LMerbecks/D38999-3MF/images/A_Shells_disconnected.jpeg

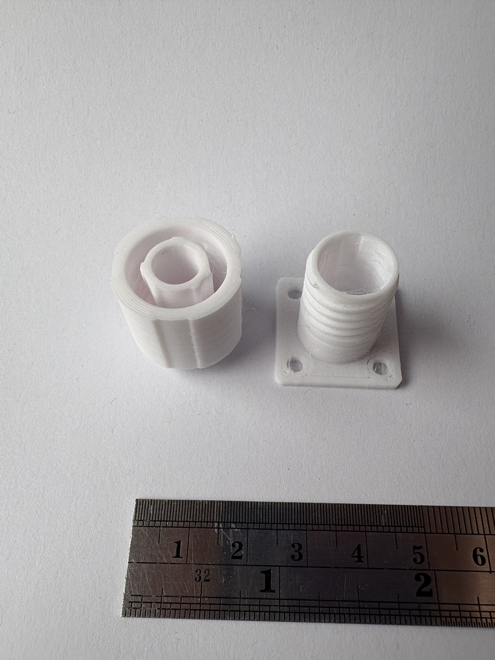
images/A_Shells_disconnected.jpeg
