LMerbecks/D38999-3MF/images/A_Shells_Mating_Dimensions.png

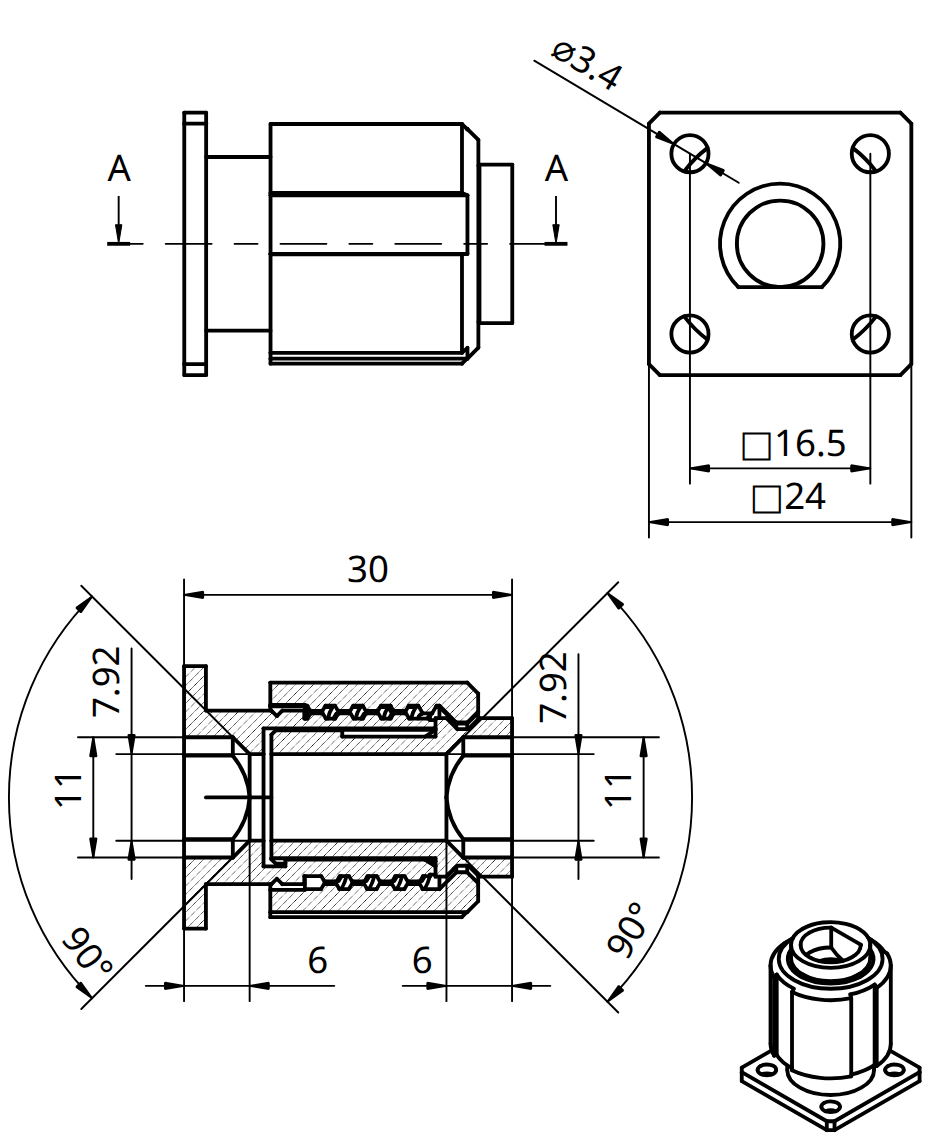
images/A_Shells_Mating_Dimensions.png
