LMerbecks/D38999-3MF/images/B_Shells_disconnected.jpeg

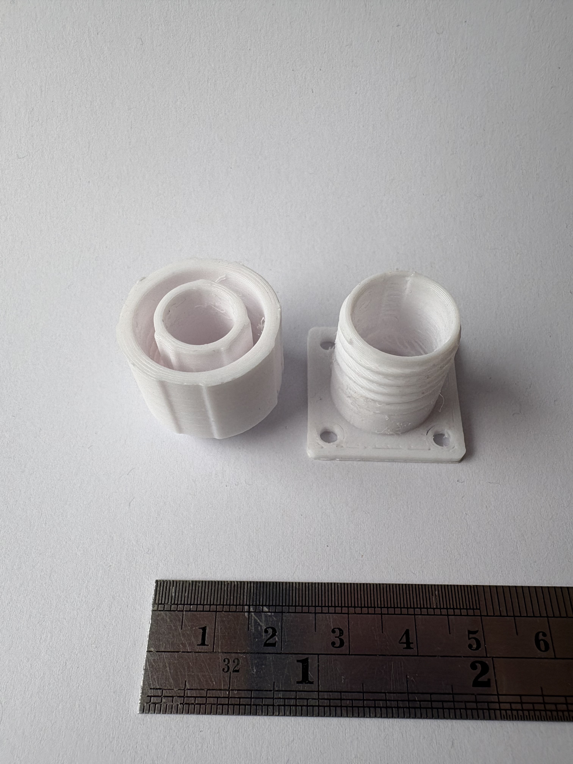
images/B_Shells_disconnected.jpeg
