LMerbecks/D38999-3MF/images/mated_front.jpg

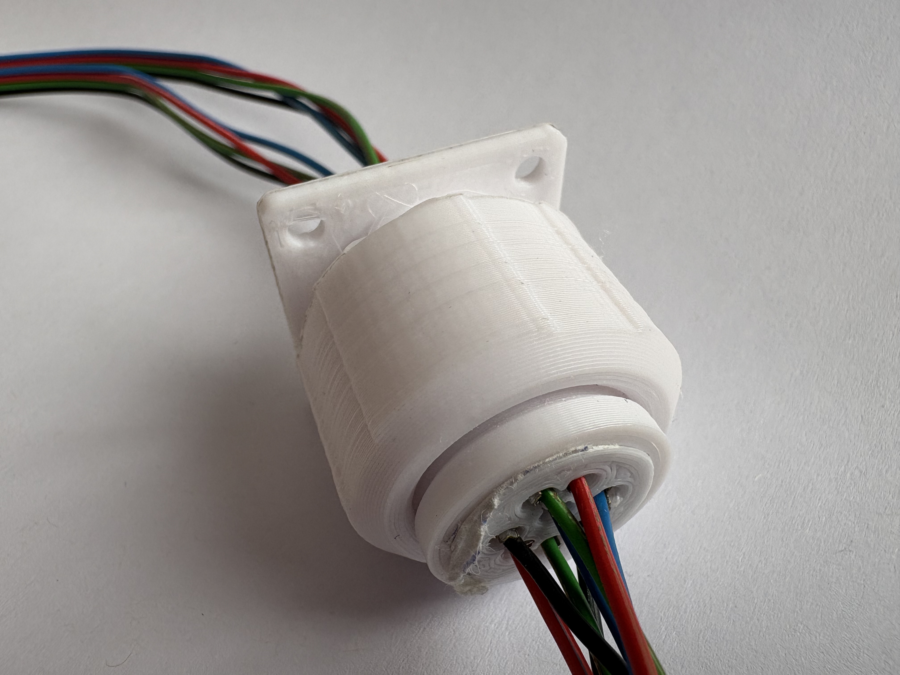
images/mated_front.jpg
